RichardAntalik/LQ079L1SX01-LT6911C-board-reverse-engineering/schematic/LQ079L1SX01_driver.kicad_sch

## KiCad design schematic/LQ079L1SX01_driver.kicad_sch (2025-09-06)

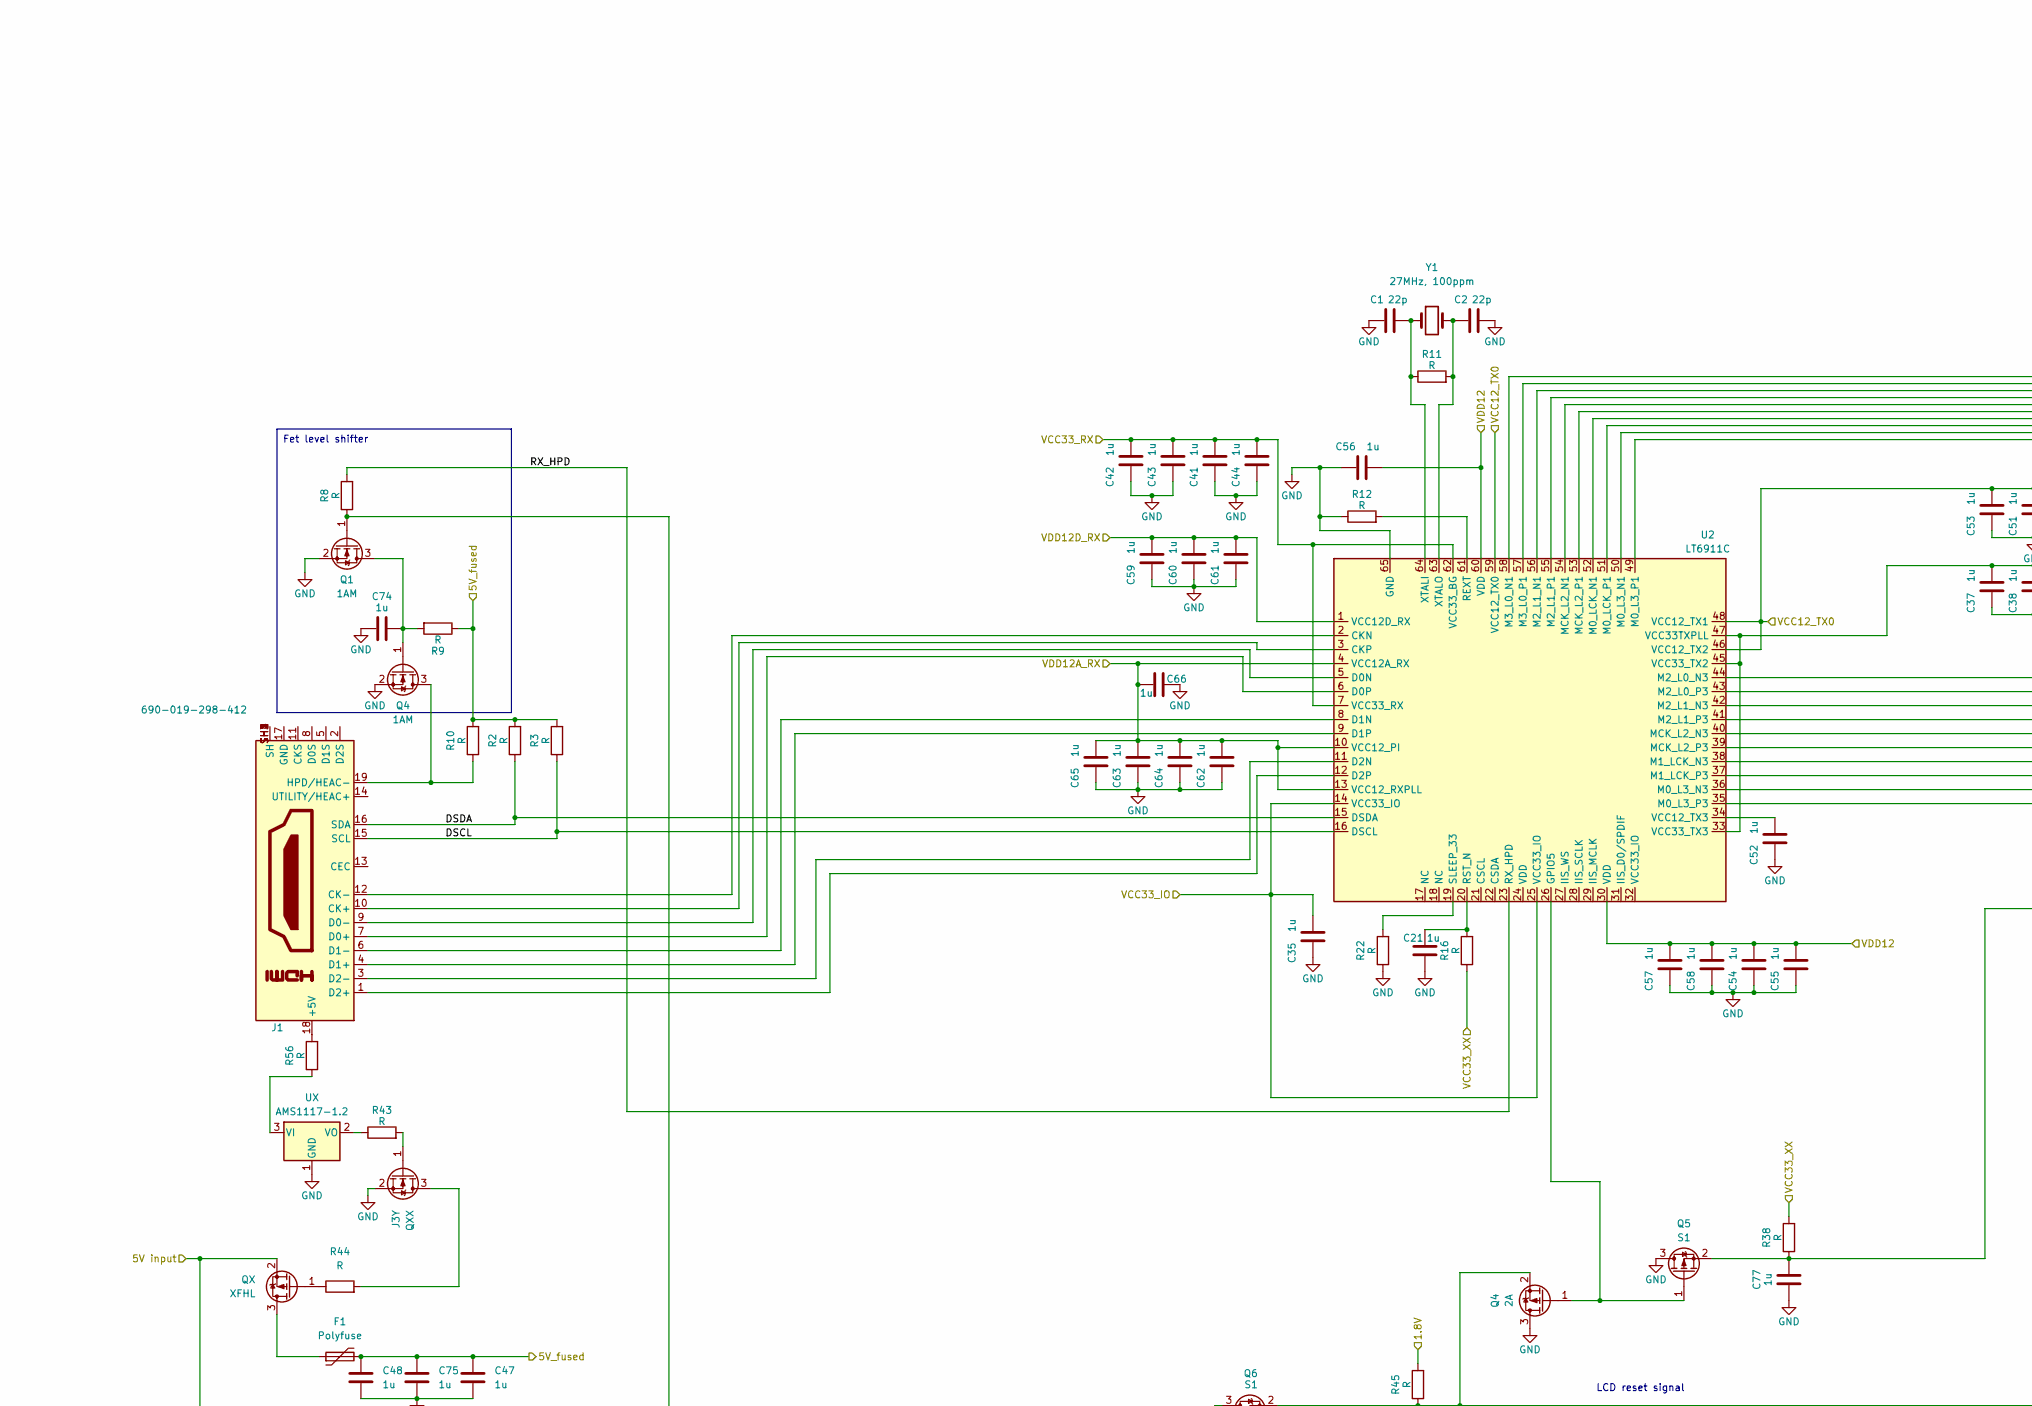
[picture p5: schematic LQ079L1SX01_driver.kicad_sch, part in row 1, column 1]

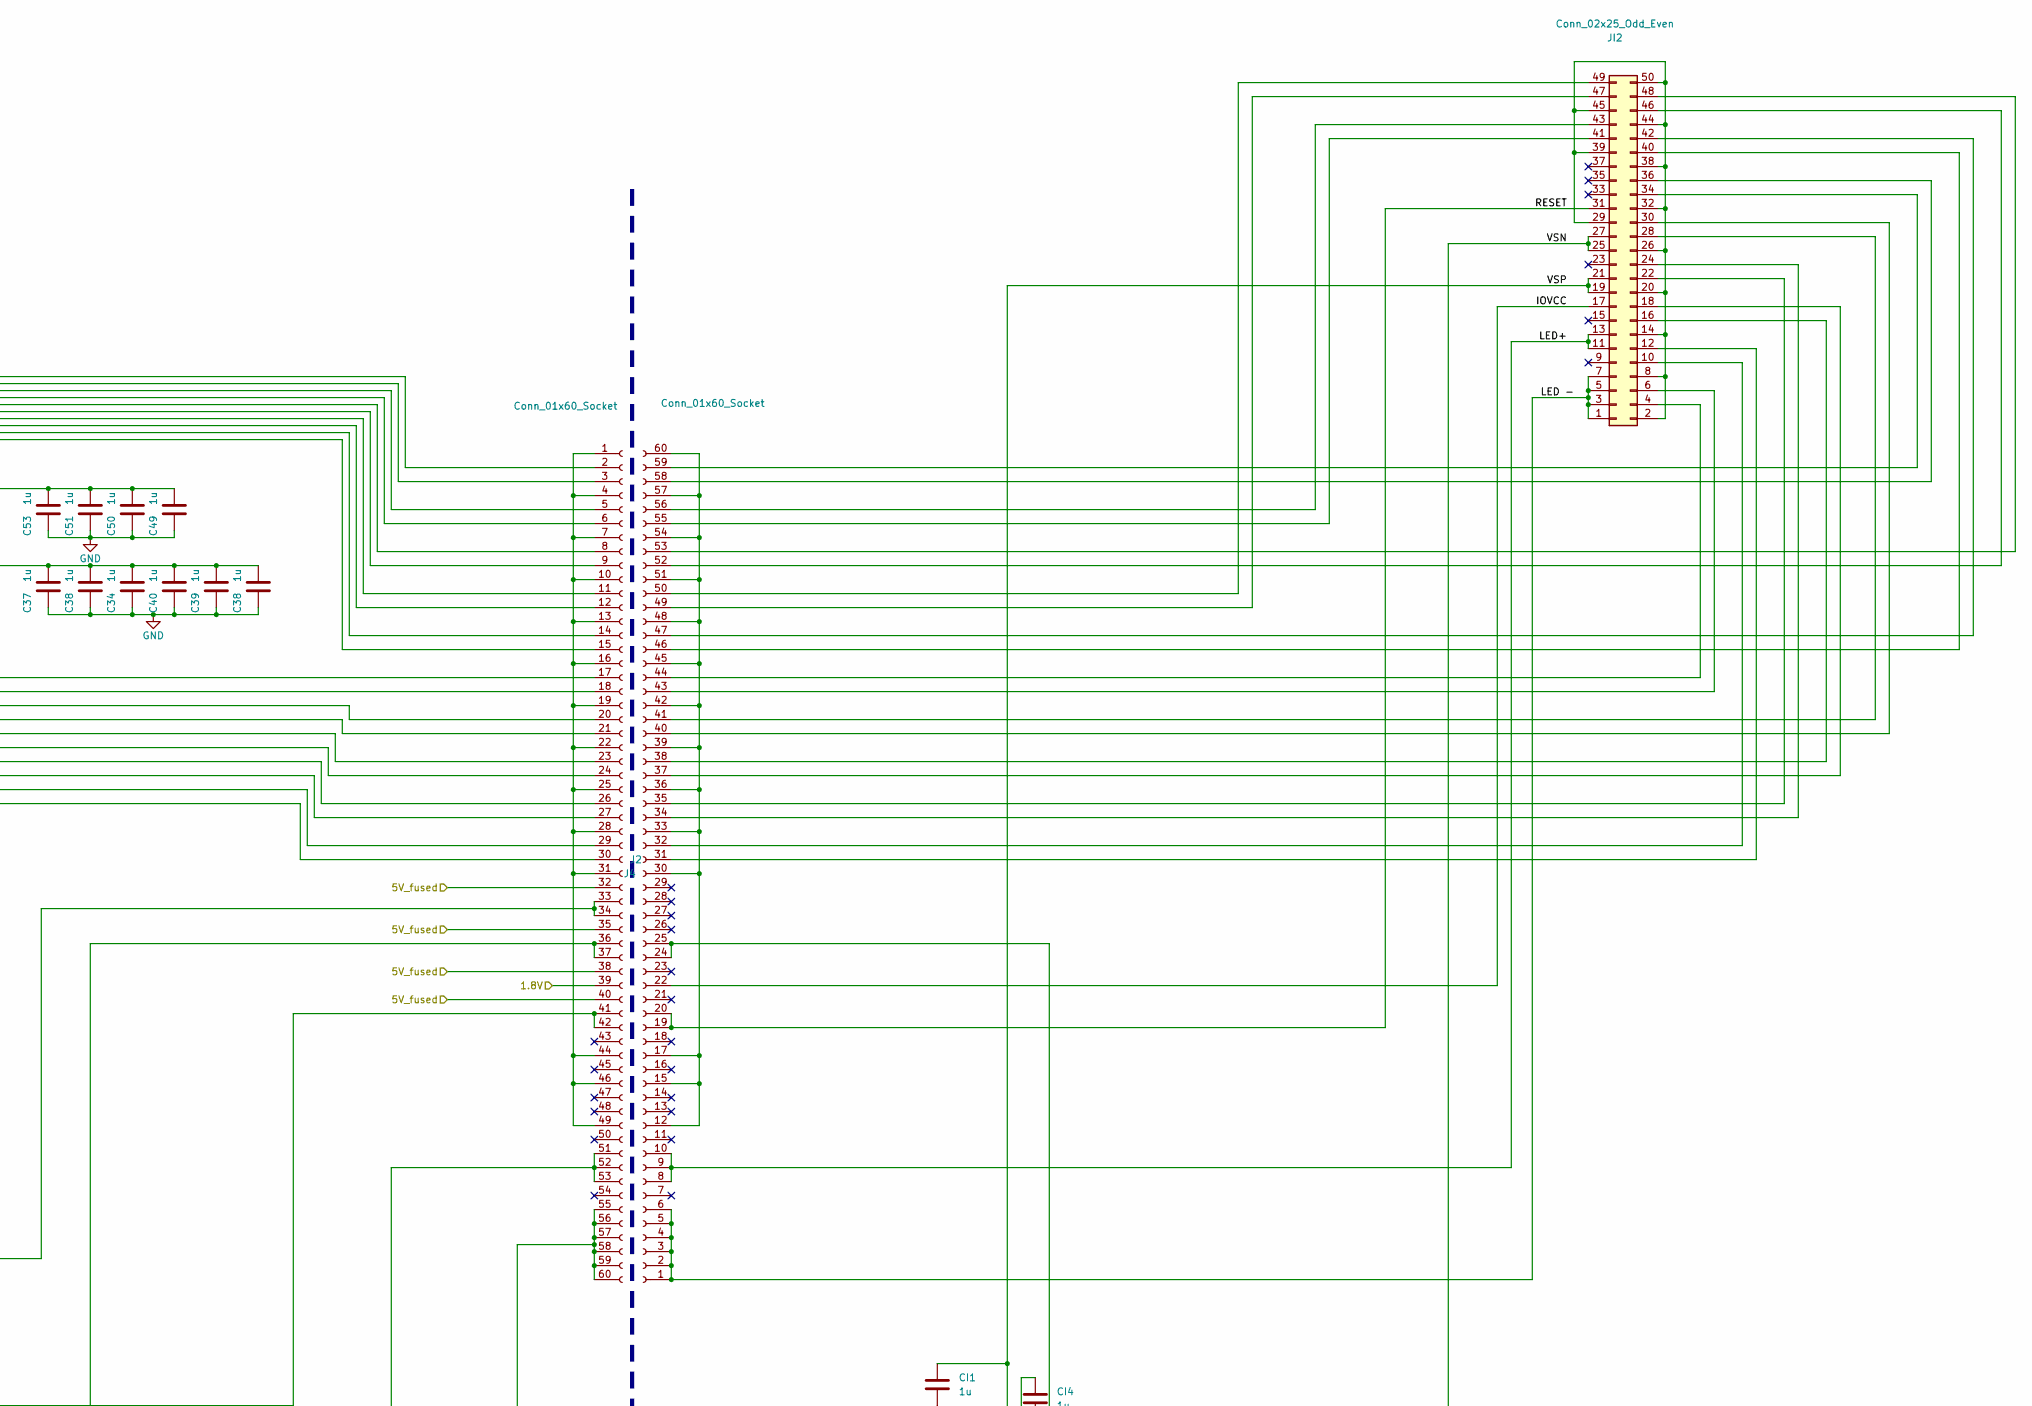
[picture p6: schematic LQ079L1SX01_driver.kicad_sch, part in row 1, column 2]

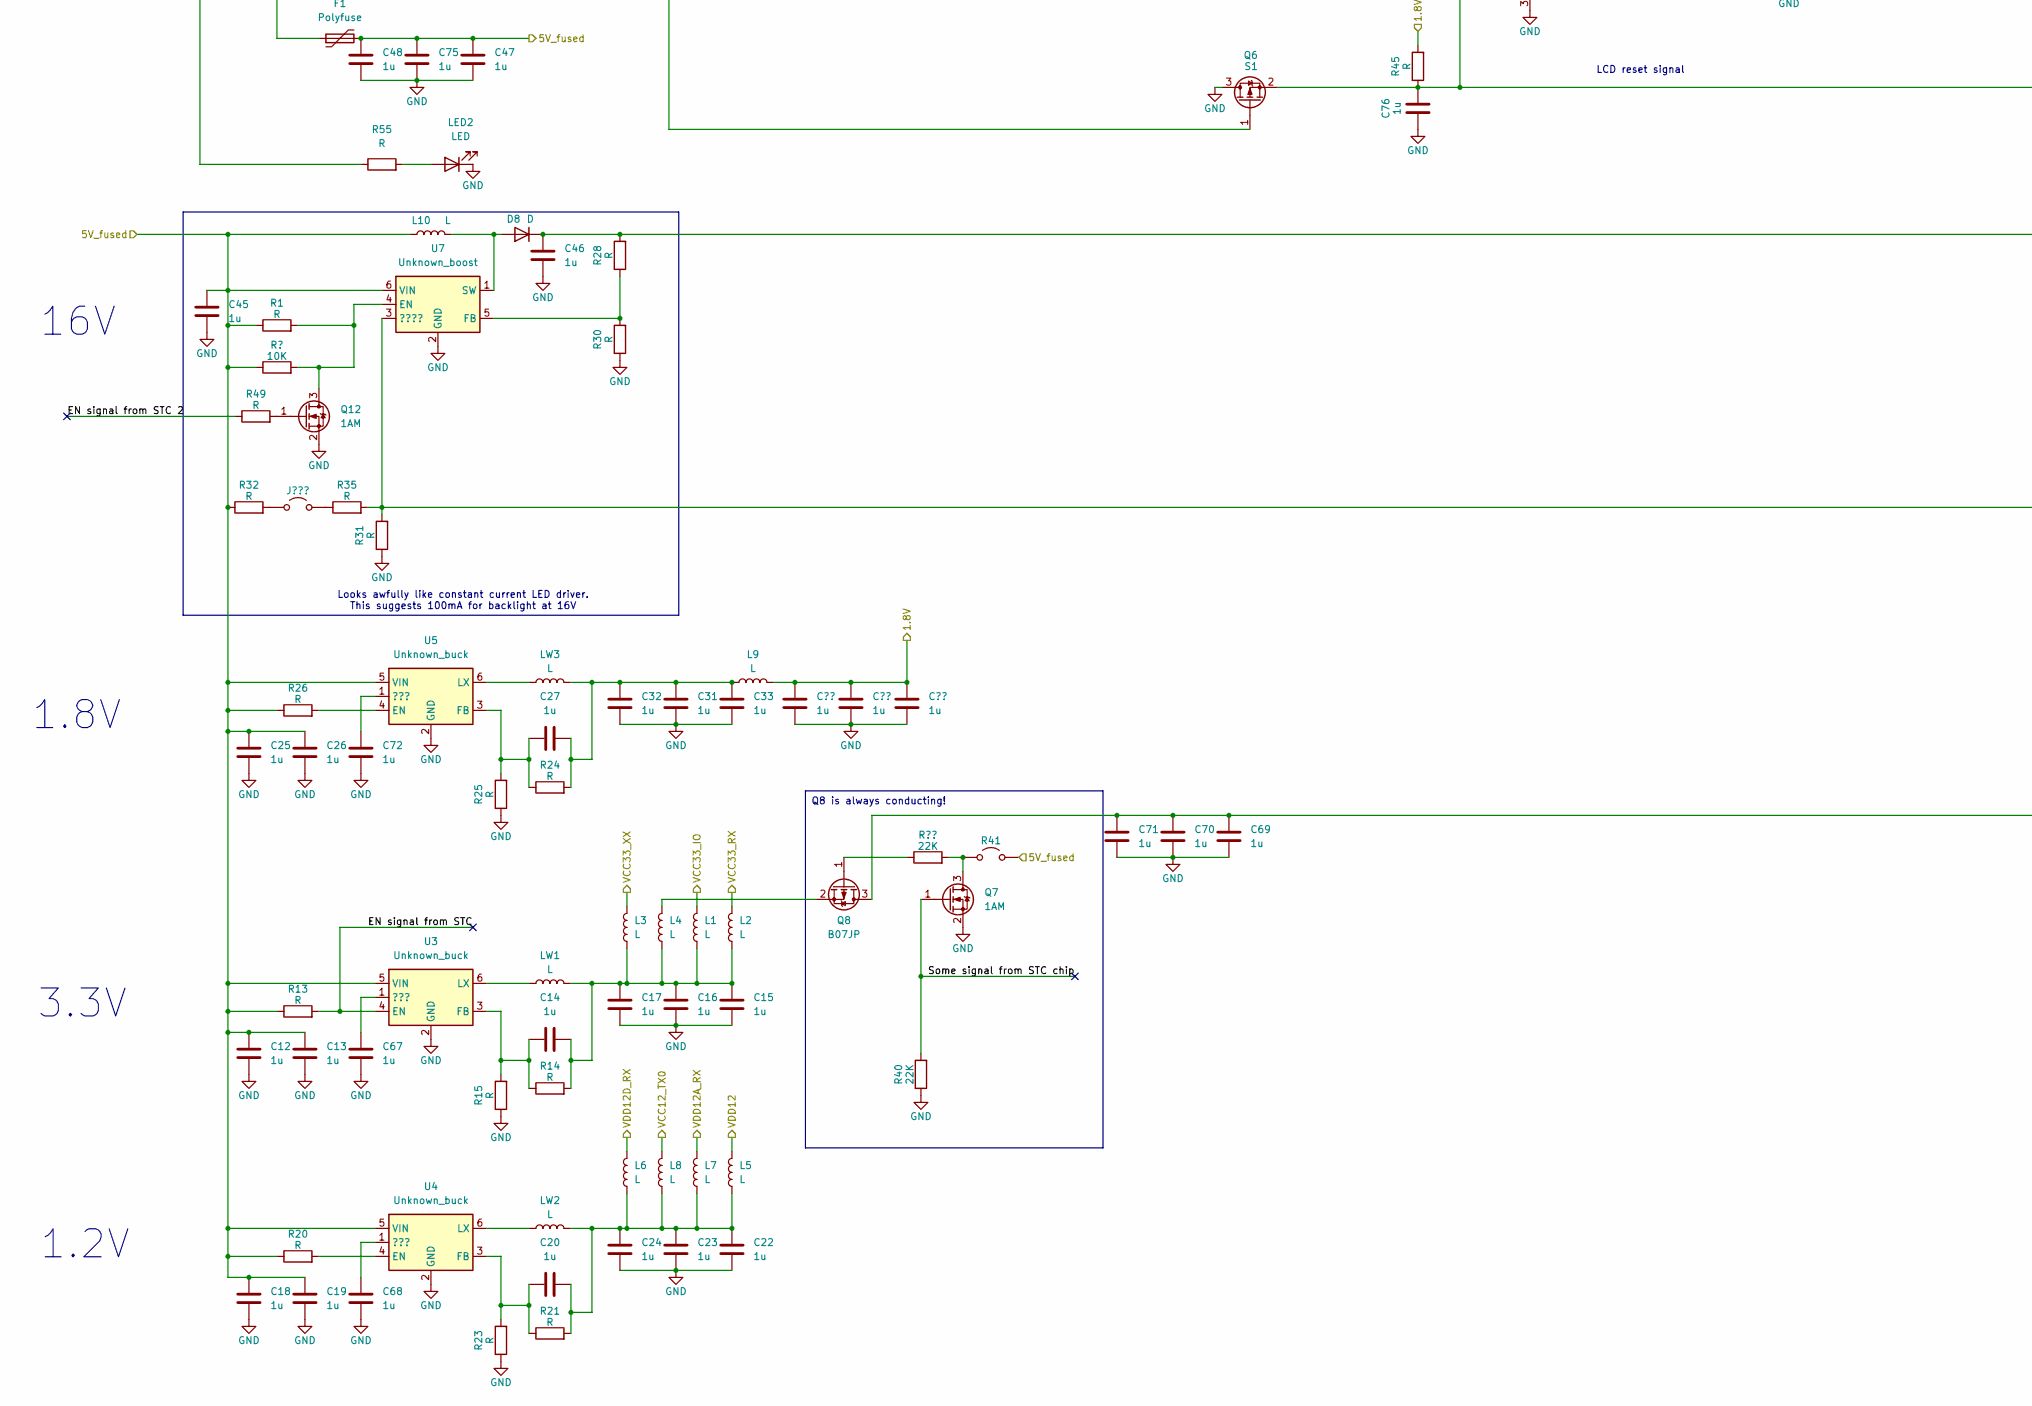
[picture p7: schematic LQ079L1SX01_driver.kicad_sch, part in row 2, column 1]

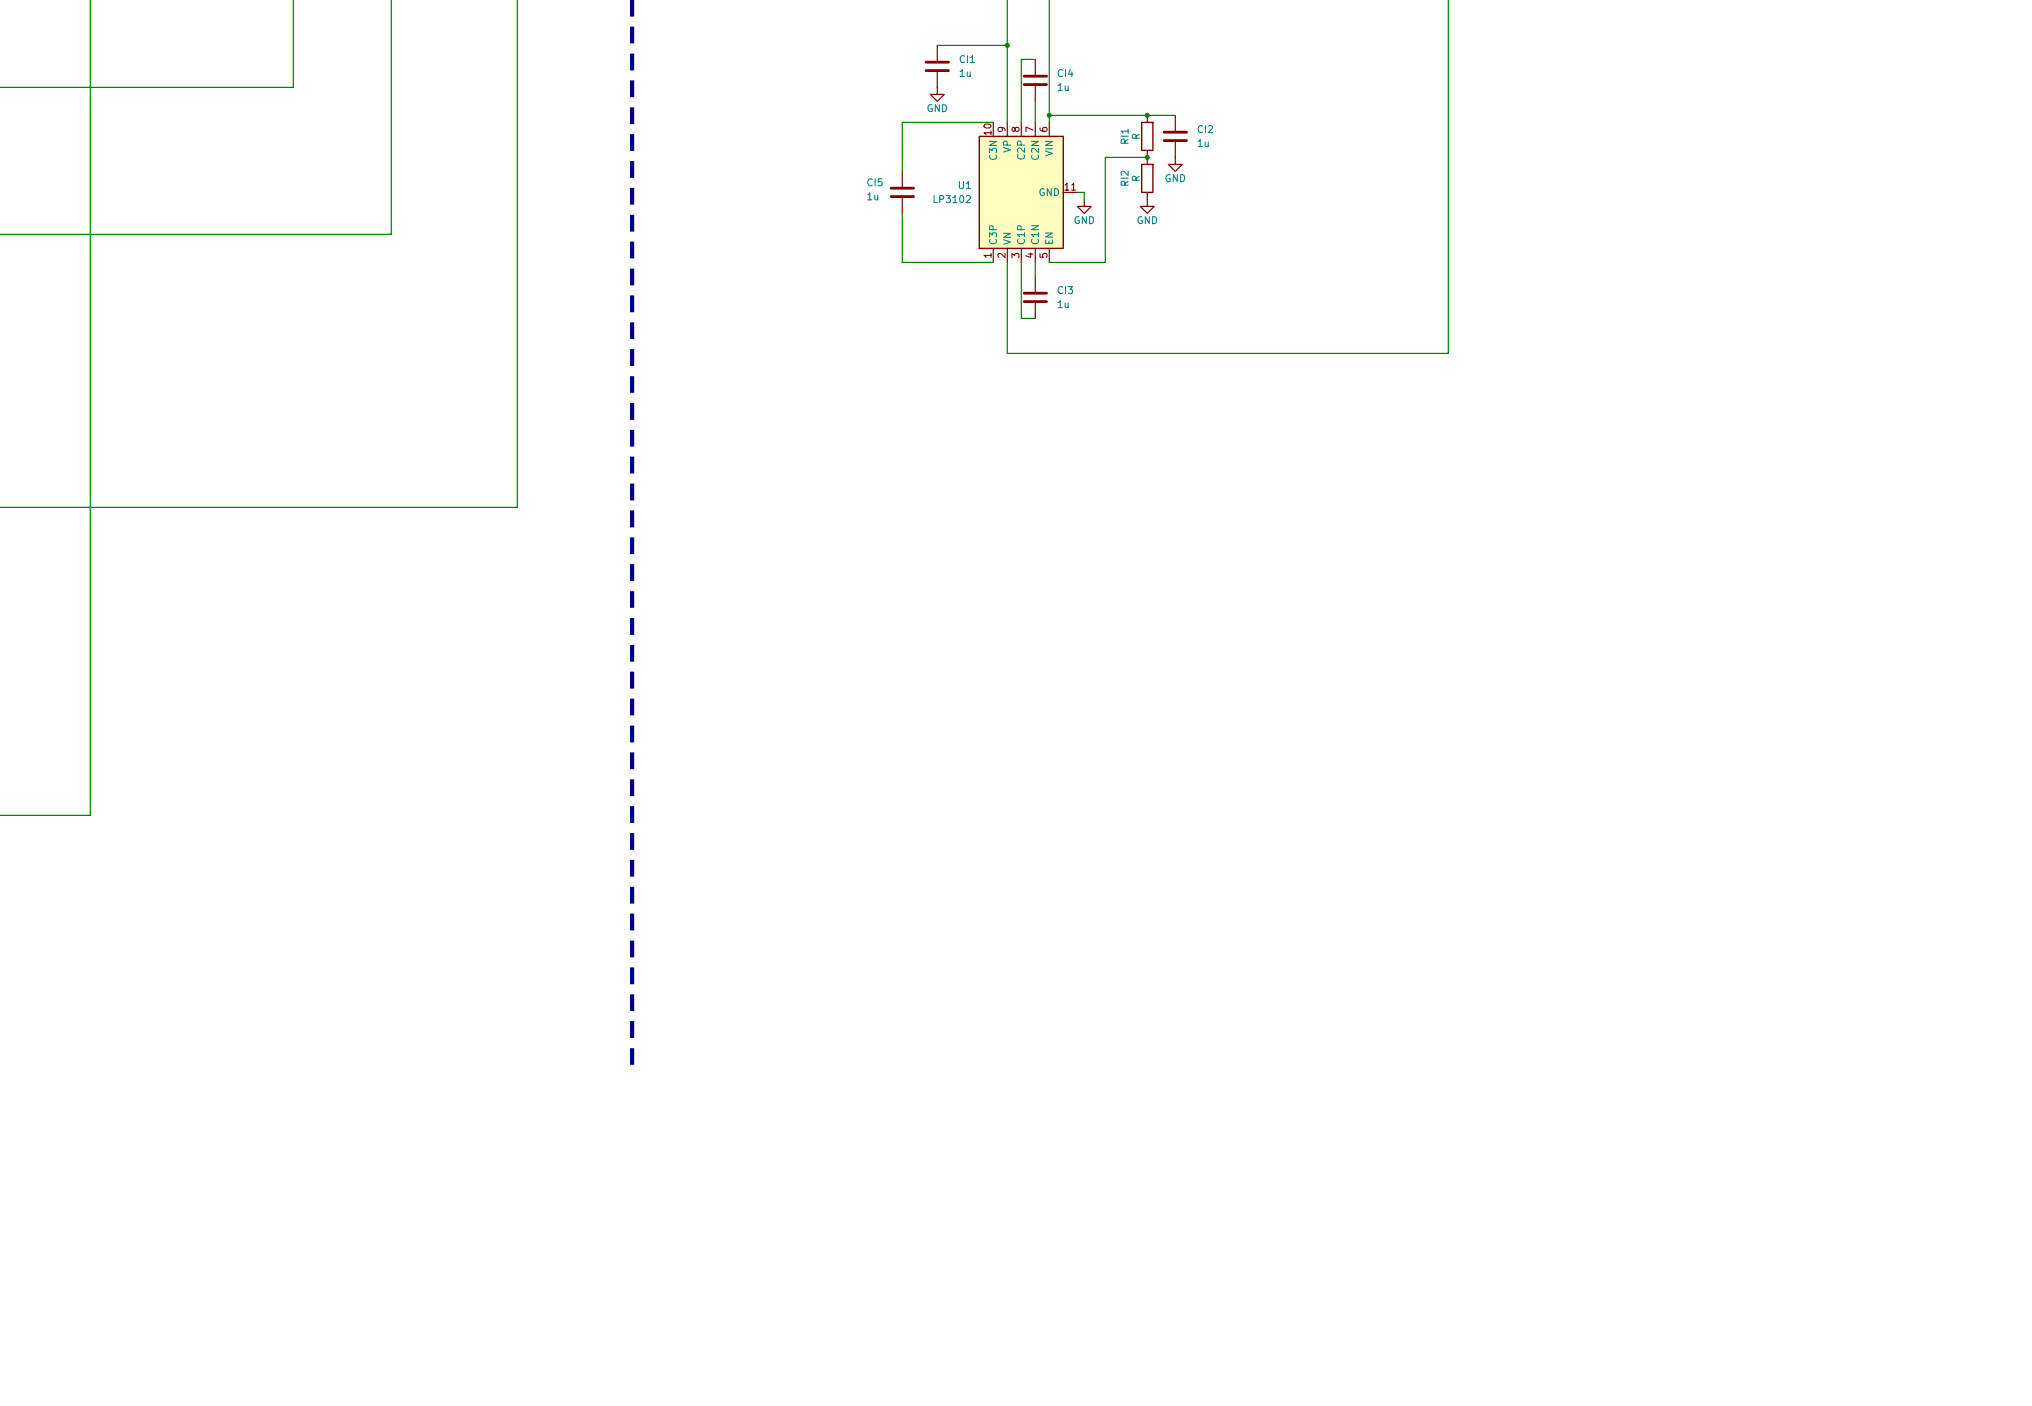
[picture p8: schematic LQ079L1SX01_driver.kicad_sch, part in row 2, column 2]

Parts:
C1, C2: 22p; C_0805_2012Metric_Pad1.18x1.45mm_HandSolder
C12, C13, C14, C15, C16, C17, C18, C19, C20, C21, C22, C23, C24, C25, C26, C27, C31, C32, C33, C34, C35, C37, C38, C39, C40, C41, C42, C43, C44, C45, C46, C47, C48, C49, C50, C51, C52, C53, C54, C55, C56, C57, C58, C59, C60, C61, C62, C63, C64, C65, C66, C67, C68, C69, C70, C71, C72, C74, C75, C76, C77: 1u; C_0805_2012Metric_Pad1.18x1.45mm_HandSolder
CI1, CI2, CI3, CI4, CI5: 1u; C_0805_2012Metric_Pad1.18x1.45mm_HandSolder
D8: D
F1: Polyfuse
J1: 690-019-298-412; EDAC 690-019-298-412; Part Description HDMI Connector, Right Angle, 19 Contact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
J2, J4: Conn_01x60_Socket
JI2: Conn_02x25_Odd_Even
L1, L2, L3, L4, L5, L6, L7, L8, L9, L10: L
LED2: LED
LW1, LW2, LW3: L
Q1, Q7, Q12: 1AM; SOT-323_SC-70
Q4: 2A; SOT-23
Q5, Q6: S1; SOT-23
Q8: B07JP; SOT-23
QX: XFHL; SOT-23
QXX: J3Y; SOT-323_SC-70
R1, R2, R3, R8, R9, R10, R11, R12, R13, R14, R15, R16, R20, R21, R22, R23, R24, R25, R26, R28, R30, R31, R32, R35, R38, R43, R44, R45, R49, R55, R56: R
R40: 22K
R41: Jumper_2_Open
RI1, RI2: R
U1: LP3102; TDFN-10-1EP_2x3mm_P0.5mm_EP0.9x2mm
U2: LT6911C; QFN-64-1EP_9x9mm_P0.5mm_EP7.3x7.3mm
U3, U4, U5: Unknown_buck; TSOT-23-6
U7: Unknown_boost; TSOT-23-6
UX: AMS1117-1.2
Y1: 27MHz, 100ppm

Connections:
1.8V: J2.39, L9.2, R45.2
5V input: QX.2 (S), R55.1
5V_fused: C12.1, C13.1, C18.1, C19.1, C25.1, C26.1, C45.1, C47.1, C48.1, C75.1, F1.2, J2.32, J2.35, J2.38, J2.40, L10.1, R1.1, R2.2, R3.2, R9.1, R10.2, R13.1, R20.1, R26.1, R32.1, R41.2 (B), U3.5 (VIN), U4.5 (VIN), U5.5 (VIN), U7.6 (VIN)
DSCL: J1.15 (SCL), R3.1, U2.16 (DSCL)
DSDA: J1.16 (SDA), R2.1, U2.15 (DSDA)
EN signal from STC: R13.2, U3.4 (EN)
EN signal from STC 2: R49.1
GND: C1.1, C2.2, C12.2, C13.2, C15.2, C16.2, C17.2, C18.2, C19.2, C21.2, C22.2, C23.2, C24.2, C25.2, C26.2, C31.2, C32.2, C33.2, C34.1, C35.1, C37.1, C38.1, C39.1, C40.1, C41.1, C42.1, C43.1, C44.1, C45.2, C46.2, C47.2, C48.2, C49.1, C50.1, C51.1, C52.1, C53.1, C54.1, C55.1, C56.1, C57.1, C58.1, C59.1, C60.1, C61.1, C62.1, C63.1, C64.1, C65.1, C66.1, C67.2, C68.2, C69.2, C70.2, C71.2, C72.2, C74.1, C75.2, C76.1, C77.1, CI1.2, CI2.2, LED2.1 (K), Q1.2 (S), Q4.2 (S), Q4.3 (D), Q5.3 (D), Q6.3 (D), Q7.2 (S), Q12.2 (S), QXX.2 (S), R12.1, R15.1, R22.1, R23.1, R25.1, R30.1, R31.1, R40.1, RI2.1, U1.11 (GND), U2.65 (GND), U3.2 (GND), U4.2 (GND), U5.2 (GND), U7.2 (GND), UX.1 (GND)
IOVCC: J4.22, JI2.17
LED -: J4.1, J4.2, J4.3, J4.4, J4.5, J4.6, JI2.1, JI2.3, JI2.5, JI2.7
LED+: J4.8, J4.9, J4.10, JI2.11, JI2.13
unnamed: C1.2, R11.1, U2.64 (XTALI), Y1.1
unnamed: C2.1, R11.2, U2.63 (XTALO), Y1.2
unnamed: C14.1, R14.1, R15.2, U3.3 (FB)
unnamed: C14.2, C15.1, C16.1, C17.1, L1.1, L2.1, L3.1, L4.1, LW1.2, R14.2
unnamed: C20.1, R21.1, R23.2, U4.3 (FB)
unnamed: C20.2, C22.1, C23.1, C24.1, L5.1, L6.1, L7.1, L8.1, LW2.2, R21.2
unnamed: C21.1, R16.2, U2.20 (RST_N)
unnamed: C27.1, R24.1, R25.2, U5.3 (FB)
unnamed: C27.2, C31.1, C32.1, C33.1, L9.1, LW3.2, R24.2
unnamed: C34.2, C37.2, C38.2, C39.2, C40.2, U2.33 (VCC33_TX3), U2.45 (VCC33_TX2), U2.47 (VCC33TXPLL)
unnamed: C46.1, D8.1 (K), J2.51, J2.52, J2.53, R28.2
unnamed: C52.2, U2.34 (VCC12_TX3)
unnamed: C67.1, U3.1 (???)
unnamed: C68.1, U4.1 (???)
unnamed: C69.1, C70.1, C71.1, J2.36, J2.37, Q8.3 (D)
unnamed: C72.1, U5.1 (???)
unnamed: C74.2, Q1.3 (D), Q4.1 (G), R9.2
unnamed: C76.2, J2.41, J2.42, Q4.2 (S), Q6.2 (S), R45.1
unnamed: C77.2, J2.33, J2.34, Q5.2 (S), R38.1
unnamed: CI2.1, J4.24, J4.25, RI1.2, U1.6 (VIN)
unnamed: CI3.1, U1.4 (C1N)
unnamed: CI3.2, U1.3 (C1P)
unnamed: CI4.1, U1.8 (C2P)
unnamed: CI4.2, U1.7 (C2N)
unnamed: CI5.1, U1.1 (C3P)
unnamed: CI5.2, U1.10 (C3N)
unnamed: D8.2 (A), L10.2, U7.1 (SW)
unnamed: F1.1, QX.3 (D)
unnamed: J1.1 (D2+), U2.12 (D2P)
unnamed: J1.3 (D2-), U2.11 (D2N)
unnamed: J1.4 (D1+), U2.9 (D1P)
unnamed: J1.6 (D1-), U2.8 (D1N)
unnamed: J1.7 (D0+), U2.6 (D0P)
unnamed: J1.9 (D0-), U2.5 (D0N)
unnamed: J1.10 (CK+), U2.3 (CKP)
unnamed: J1.12 (CK-), U2.2 (CKN)
unnamed: J1.18 (+5V), R56.2
unnamed: J1.19 (HPD/HEAC-), Q4.3 (D), R10.1
unnamed: J1.SH1 (SH), J1.SH2 (SH), J1.SH3 (SH), J1.SH4 (SH)
unnamed: J2.1, J2.4, J2.7, J2.10, J2.13, J2.16, J2.19, J2.22, J2.25, J2.28, J2.31, J2.44, J2.46, J2.49
unnamed: J2.2, U2.58 (M3_L0_N1)
unnamed: J2.3, U2.57 (M3_L0_P1)
unnamed: J2.5, U2.56 (M2_L1_N1)
unnamed: J2.6, U2.55 (M2_L1_P1)
unnamed: J2.8, U2.54 (MCK_L2_N1)
unnamed: J2.9, U2.53 (MCK_L2_P1)
unnamed: J2.11, U2.52 (M0_LCK_N1)
unnamed: J2.12, U2.51 (M0_LCK_P1)
unnamed: J2.14, U2.50 (M0_L3_N1)
unnamed: J2.15, U2.49 (M0_L3_P1)
unnamed: J2.17, U2.44 (M2_L0_N3)
unnamed: J2.18, U2.43 (M2_L0_P3)
unnamed: J2.20, U2.42 (M2_L1_N3)
unnamed: J2.21, U2.41 (M2_L1_P3)
unnamed: J2.23, U2.40 (MCK_L2_N3)
unnamed: J2.24, U2.39 (MCK_L2_P3)
unnamed: J2.26, U2.38 (M1_LCK_N3)
unnamed: J2.27, U2.37 (M1_LCK_P3)
unnamed: J2.29, U2.36 (M0_L3_N3)
unnamed: J2.30, U2.35 (M0_L3_P3)
unnamed: J2.55, J2.56, J2.57, J2.58, J2.59, J2.60, R31.2, R35.2, U7.3 (????)
unnamed: J4.12, J4.15, J4.17, J4.30, J4.33, J4.36, J4.39, J4.42, J4.45, J4.48, J4.51, J4.54, J4.57, J4.60
unnamed: J4.31, JI2.12
unnamed: J4.32, JI2.10
unnamed: J4.34, JI2.24
unnamed: J4.35, JI2.22
unnamed: J4.37, JI2.18
unnamed: J4.38, JI2.16
unnamed: J4.40, JI2.30
unnamed: J4.41, JI2.28
unnamed: J4.43, JI2.6
unnamed: J4.44, JI2.4
unnamed: J4.46, JI2.40
unnamed: J4.47, JI2.42
unnamed: J4.49, JI2.47
unnamed: J4.50, JI2.49
unnamed: J4.52, JI2.46
unnamed: J4.53, JI2.48
unnamed: J4.55, JI2.41
unnamed: J4.56, JI2.43
unnamed: J4.58, JI2.36
unnamed: J4.59, JI2.34
unnamed: JI2.2, JI2.8, JI2.14, JI2.20, JI2.26, JI2.29, JI2.32, JI2.38, JI2.39, JI2.44, JI2.45, JI2.50
unnamed: L4.2, Q8.2 (S)
unnamed: LED2.2 (A), R55.2
unnamed: LW1.1, U3.6 (LX)
unnamed: LW2.1, U4.6 (LX)
unnamed: LW3.1, U5.6 (LX)
unnamed: Q1.1 (G), Q6.1 (G), R8.1
unnamed: Q4.1 (G), Q5.1 (G), U2.26 (GPIO5)
unnamed: Q7.3 (D), R41.1 (A)
unnamed: Q12.1 (G), R49.2
unnamed: Q12.3 (D), R1.2, U7.4 (EN)
unnamed: QX.1 (G), R44.1
unnamed: QXX.1 (G), R43.2
unnamed: QXX.3 (D), R44.2
unnamed: R12.2, U2.61 (REXT)
unnamed: R20.2, U4.4 (EN)
unnamed: R22.2, U2.19 (SLEEP_33)
unnamed: R26.2, U5.4 (EN)
unnamed: R28.1, R30.2, U7.5 (FB)
unnamed: R43.1, UX.2 (VO)
unnamed: R56.1, UX.3 (VI)
unnamed: RI1.1, RI2.2, U1.5 (EN)
RESET: J4.19, J4.20, JI2.31
RX_HPD: R8.2, U2.23 (RX_HPD)
Some signal from STC chip: Q7.1 (G), R40.2
VCC12_TX0: C49.2, C50.2, C51.2, C53.2, L8.2, U2.46 (VCC12_TX2), U2.48 (VCC12_TX1), U2.59 (VCC12_TX0)
VCC33_IO: C35.2, L1.2, U2.14 (VCC33_IO), U2.25 (VCC33_IO)
VCC33_RX: C41.2, C42.2, C43.2, C44.2, L2.2, U2.7 (VCC33_RX), U2.62 (VCC33_BG)
VCC33_XX: L3.2, R16.1, R38.2
VDD12: C54.2, C55.2, C56.2, C57.2, C58.2, L5.2, U2.30 (VDD), U2.60 (VDD)
VDD12A_RX: C62.2, C63.2, C64.2, C65.2, C66.2, L7.2, U2.4 (VCC12A_RX), U2.10 (VCC12_PI), U2.13 (VCC12_RXPLL)
VDD12D_RX: C59.2, C60.2, C61.2, L6.2, U2.1 (VCC12D_RX)
VSN: JI2.25, JI2.27, U1.2 (VN)
VSP: CI1.1, JI2.19, JI2.21, U1.9 (VP)

Notes on the sheet:
Fet level shifter
Q8 is always conducting!
1.2V
LCD reset signal
1.8V
16V
3.3V
Looks awfully like constant current LED driver. This suggests 100mA for backlight at 16V
